BUNPC/ninjaCap2/stl/elements/#NFDSO/grommet.STL

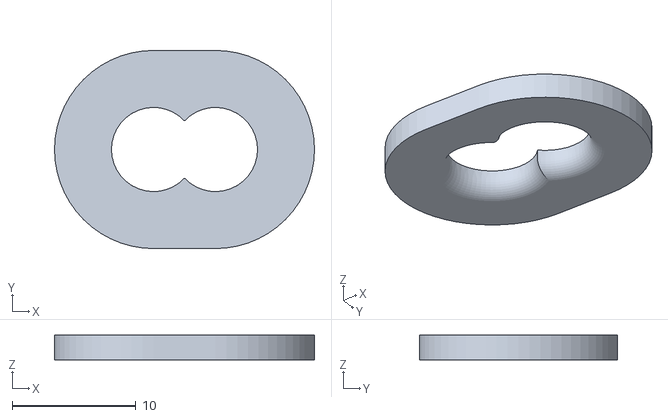
[picture p52: CAD file, 2021-02-07, an earlier design]
stl/elements/#NFDSO/grommet.STL
21.0 x 16.0 x 2.00
